Datafordev/OSBH/hardware/etching/etching_top.png

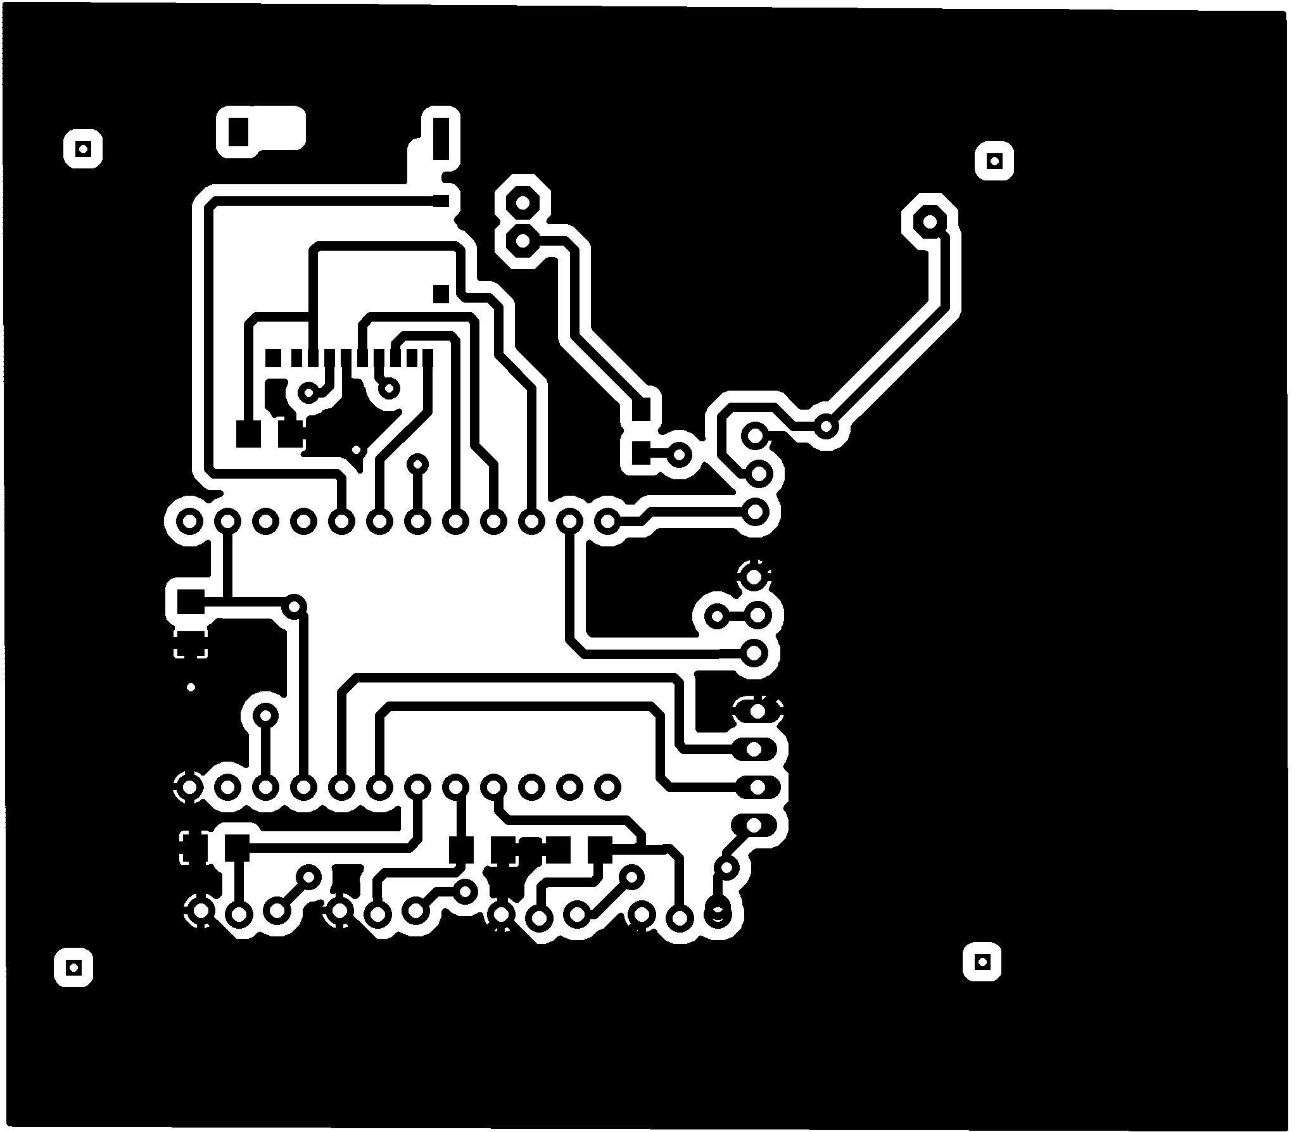
hardware/etching/etching_top.png
